eparadis/pill_bottle_insert/images/IMG_2484.jpeg

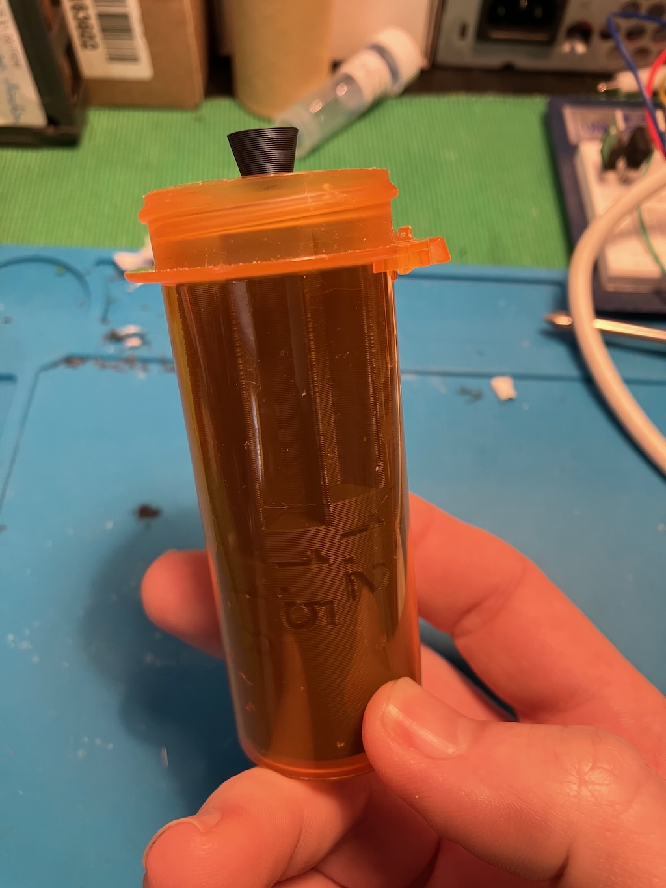
images/IMG_2484.jpeg
