eparadis/pill_bottle_insert/images/IMG_2485.jpeg

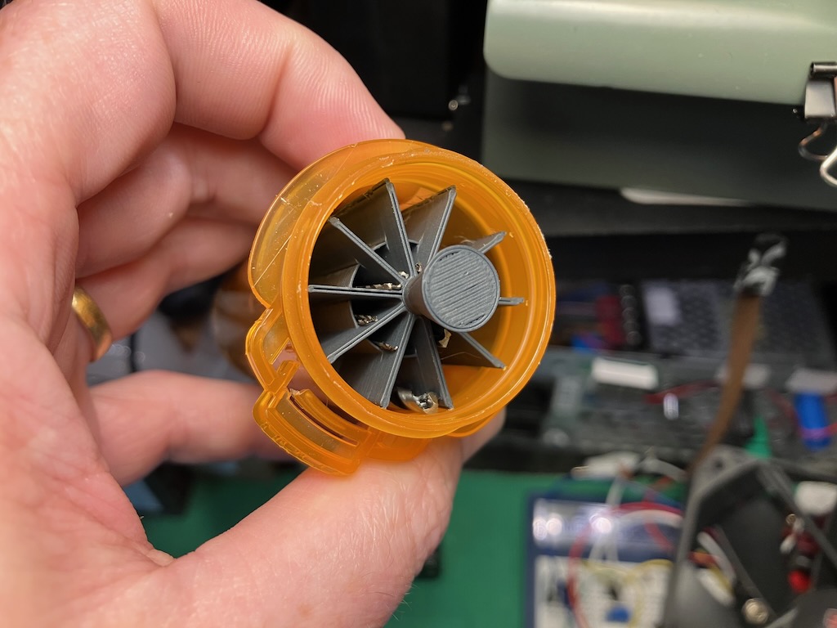
images/IMG_2485.jpeg
