eparadis/pill_bottle_insert/images/IMG_2487.jpeg

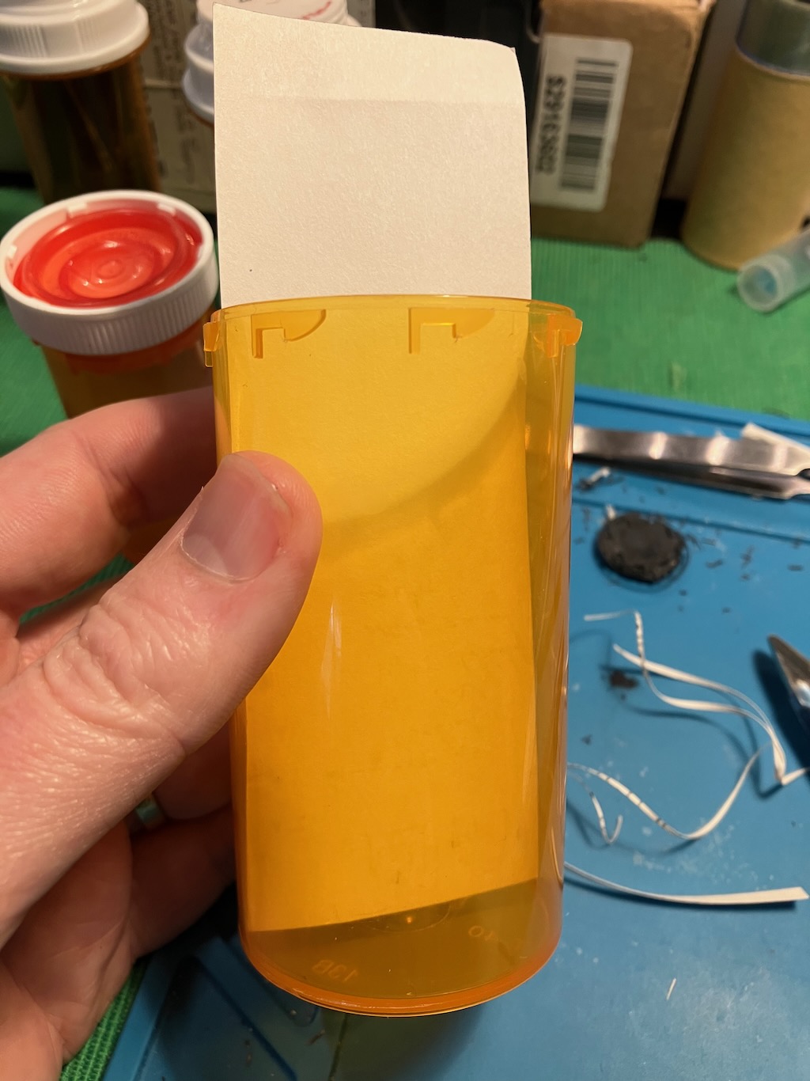
images/IMG_2487.jpeg
